VoronManiac/Maniac-Chamber-Lighting/STL/Voron300/LEDBar300.stl

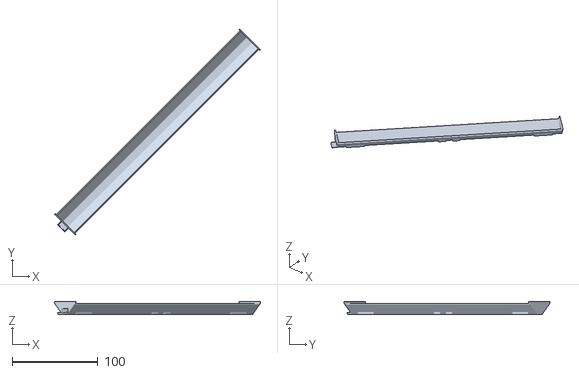
[picture p34: CAD file, 2023-03-27]
STL/Voron300/LEDBar300.stl
239.6 x 239.6 x 14.7
