VoronManiac/Maniac-Chamber-Lighting/STL/Voron350/LEDBar400.stl

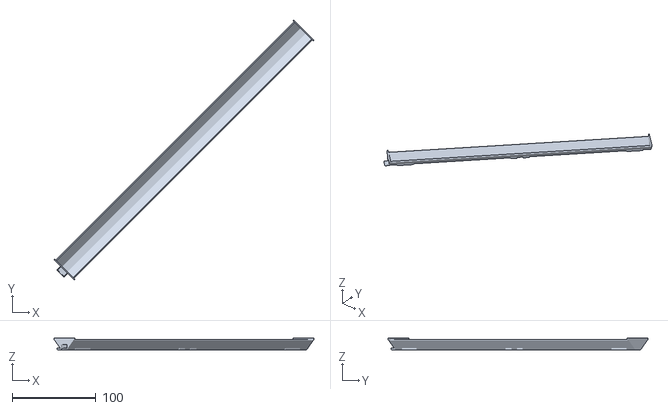
[picture p35: CAD file, 2023-03-27]
STL/Voron350/LEDBar400.stl
310.3 x 310.3 x 14.7
