VoronManiac/Maniac-Chamber-Lighting/CAD/LEDbar_15deg.step

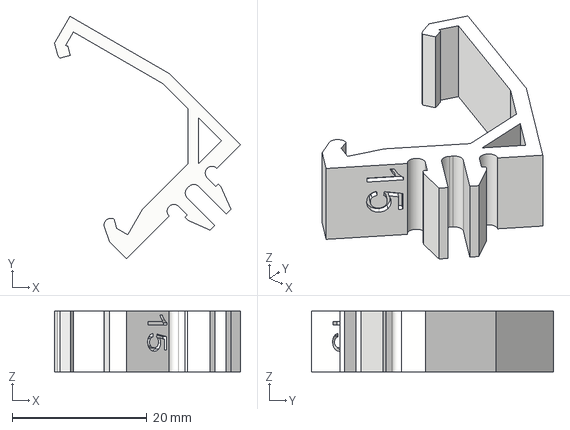
[picture p36: CAD file, 2023-03-28]
CAD/LEDbar_15deg.step
27.6 x 36.0 x 9.00 mm
