VoronManiac/Maniac-Chamber-Lighting/STL/Voron250/LEDBar250.stl

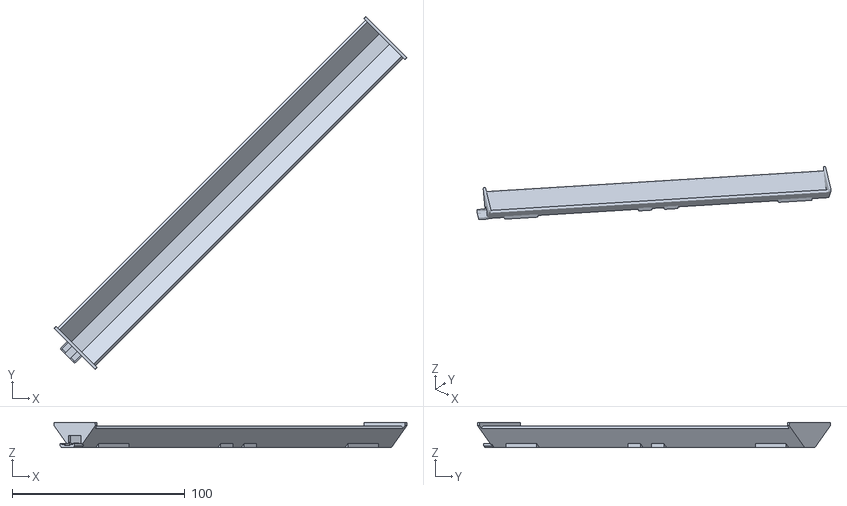
[picture p37: CAD file, 2023-03-27]
STL/Voron250/LEDBar250.stl
204.2 x 204.2 x 14.7
