VoronManiac/Maniac-Chamber-Lighting/STL/Voron300/LEDdiffuser350.stl

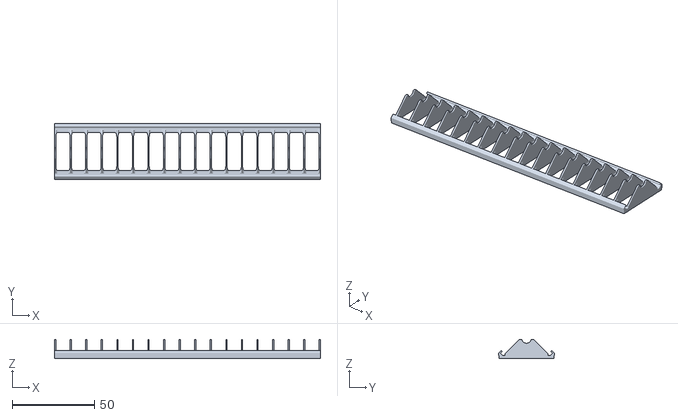
[picture p38: CAD file, 2023-03-27]
STL/Voron300/LEDdiffuser350.stl
161.9 x 34.1 x 11.8
