VoronManiac/Maniac-Chamber-Lighting/STL/Voron350/SlotCoverVert200.stl

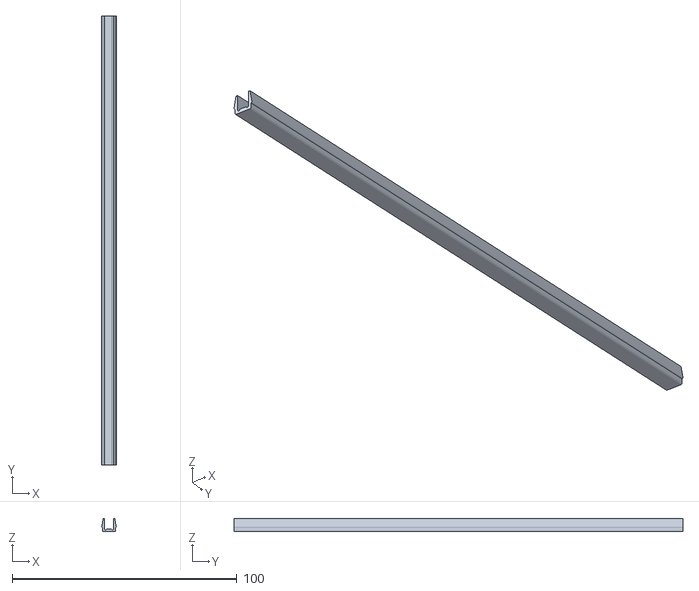
[picture p39: CAD file, 2023-03-23]
STL/Voron350/SlotCoverVert200.stl
6.50 x 200.0 x 6.00
