VoronManiac/Maniac-Chamber-Lighting/STL/Voron350/SlotCoverVert287.stl

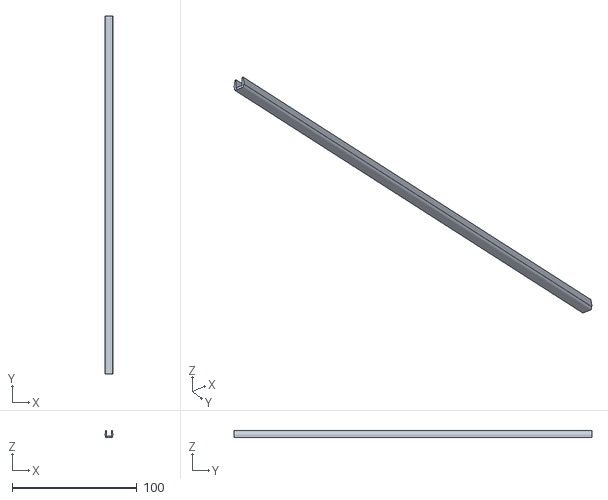
[picture p40: CAD file, 2023-03-23]
STL/Voron350/SlotCoverVert287.stl
6.50 x 287.0 x 6.00
