VoronManiac/Maniac-Chamber-Lighting/STL/Common/LEDClip45.stl

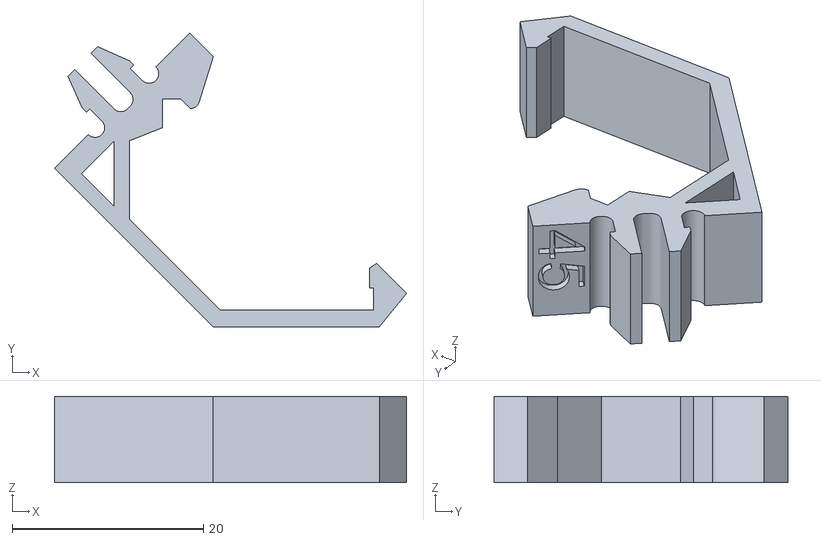
[picture p41: CAD file, 2023-03-27]
STL/Common/LEDClip45.stl
36.8 x 30.7 x 9.00
