VoronManiac/Maniac-Chamber-Lighting/STL/Voron250/LEDdiffuser300.stl

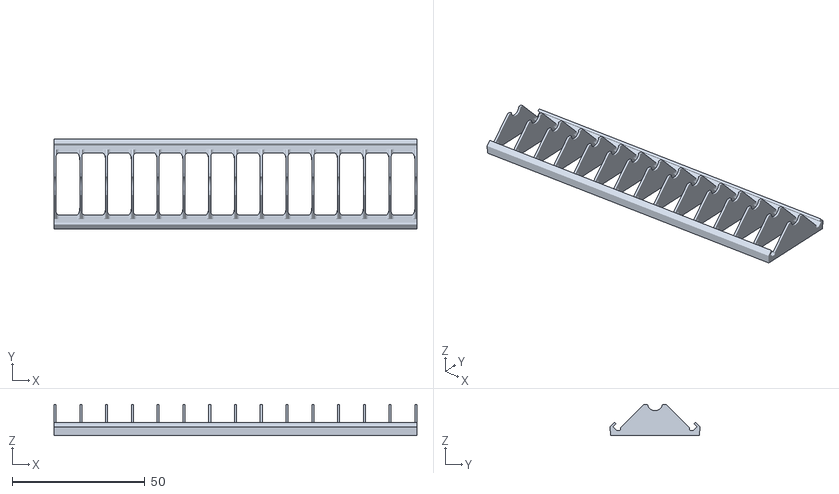
[picture p42: CAD file, 2023-03-27]
STL/Voron250/LEDdiffuser300.stl
136.9 x 34.1 x 11.8
