VoronManiac/Maniac-Chamber-Lighting/STL/Common/CornerJunctionCapLarge.stl

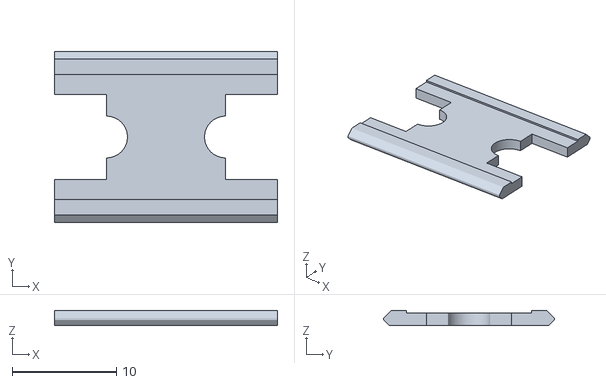
[picture p43: CAD file, 2023-03-23]
STL/Common/CornerJunctionCapLarge.stl
21.4 x 16.4 x 1.40
