VoronManiac/Maniac-Chamber-Lighting/STL/Common/CornerJunctionBoxMirror.stl

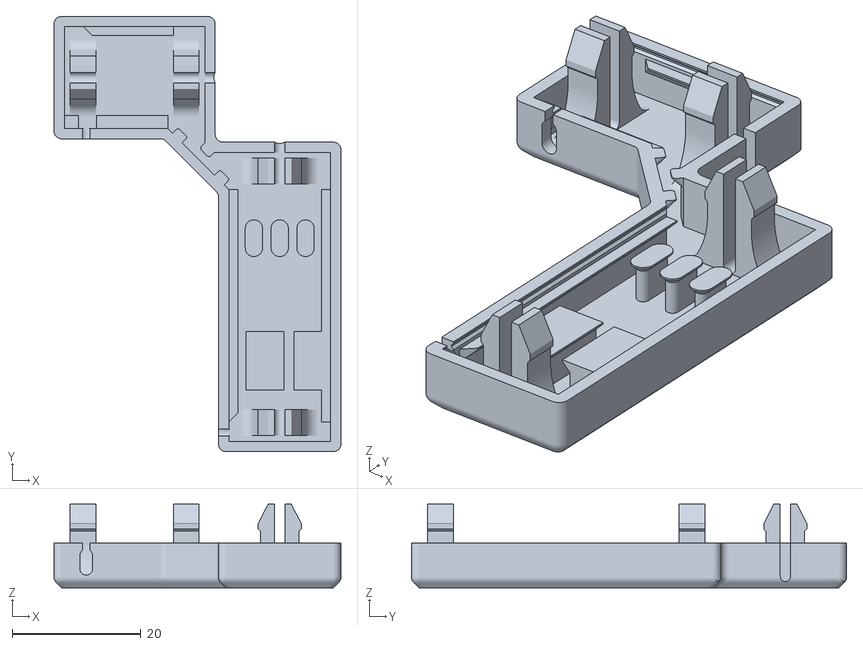
[picture p44: CAD file, 2023-03-23]
STL/Common/CornerJunctionBoxMirror.stl
44.5 x 67.5 x 13.0
