VoronManiac/Maniac-Chamber-Lighting/STL/Common/CornerJunctionCapSmall.stl

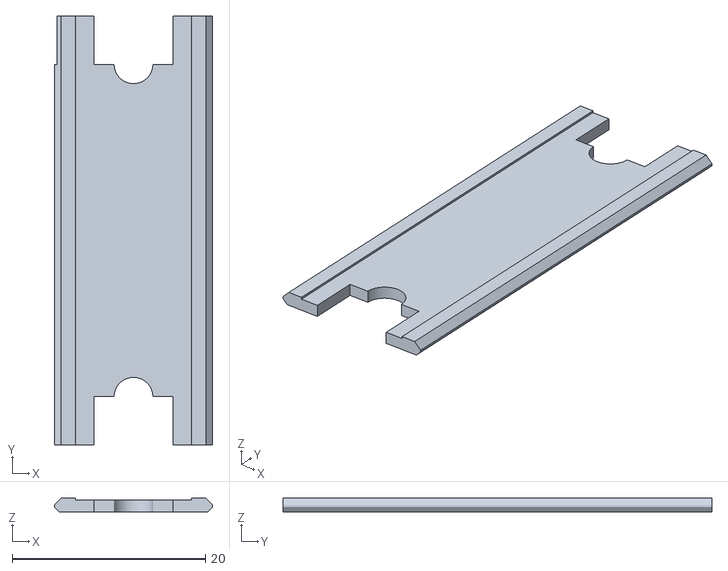
[picture p45: CAD file, 2023-03-23]
STL/Common/CornerJunctionCapSmall.stl
16.4 x 44.4 x 1.40
