VoronManiac/Maniac-Chamber-Lighting/STL/Common/LEDRetainer.stl

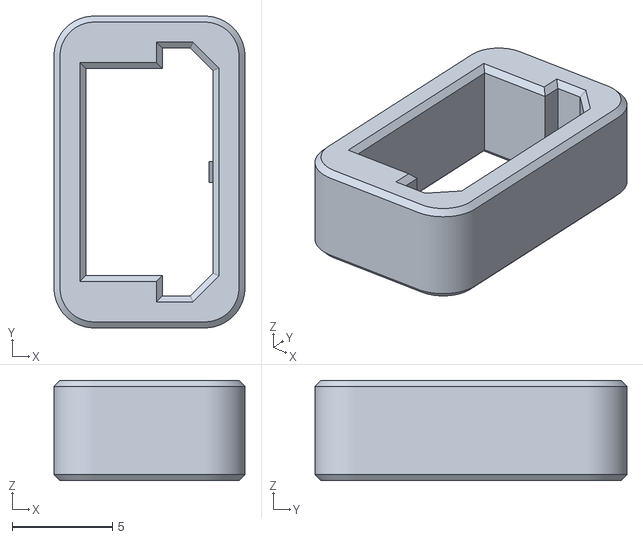
[picture p46: CAD file, 2023-03-22]
STL/Common/LEDRetainer.stl
9.52 x 15.5 x 5.00
